Capstone-Gait-Keepers/capstone/backend/serial_bridge.py

import serial
import requests
import time
from json import loads
import json

START_SIGNAL = b'BEGIN_TRANSMISSION'

def serial_bridge(serial_port='/dev/cu.usbserial-0001', baud_rate=115200):
    # Open the serial port for communication with the ESP8266.
    ser = serial.Serial(serial_port, baud_rate)
    line = ser.readline()
    while True:
        try:
            while START_SIGNAL not in line:
                line = ser.readline()
                if line:
                    print(line)
                # TODO: Need sleep to reduce CPU usage?
                time.sleep(0.05)
            line = b''
            url = ser.readline().decode().strip()
            json_data = json.loads(ser.readline().strip())
            print(f"URL: {url}\nJSON: {json_data}")
            # TODO: Validate JSON and url
            resp = requests.post(url, json=json_data)
            print(f"{resp.status_code}: {resp.text}")

        # TODO: Confirm error handling works
        except UnicodeDecodeError:
            print(f"500: Couldn't decode")



if __name__ == '__main__':
    serial_bridge()
